MatteoAlbi/robotic-arm/python/1.jpg

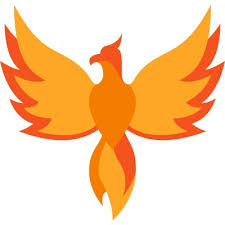
python/1.jpg
