MatteoAlbi/robotic-arm/solid works arm design/cuscinetto a sfera.SLDPRT

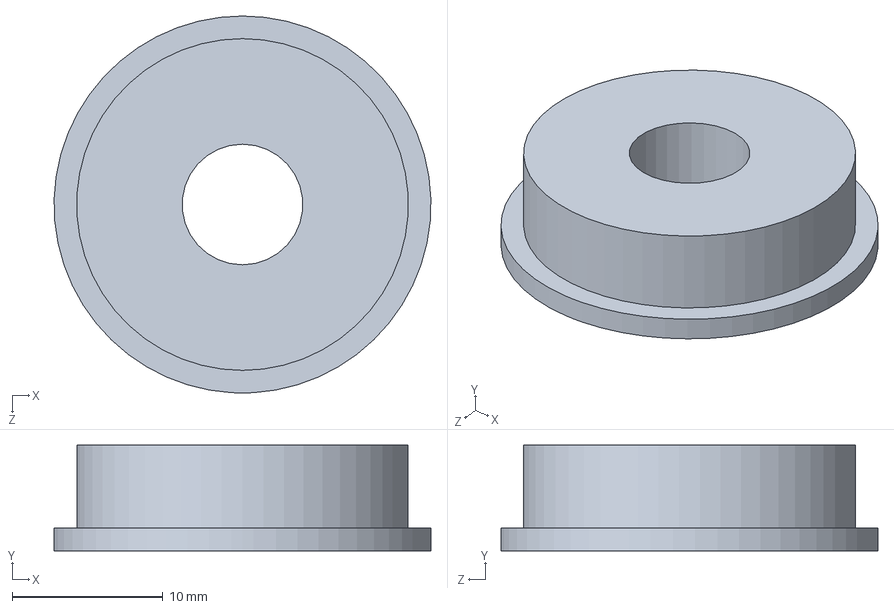
[picture p22: CAD file, 2018-10-06]
solid works arm design/cuscinetto a sfera.SLDPRT
25.0 x 7.00 x 25.0 mm
