MatteoAlbi/robotic-arm/solid works arm design/pinza motore.SLDPRT

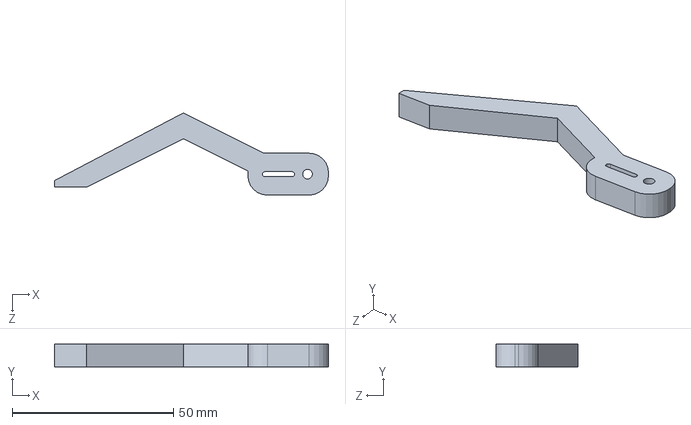
[picture p23: CAD file, 2018-10-06]
solid works arm design/pinza motore.SLDPRT
85.0 x 7.00 x 25.5 mm
