MatteoAlbi/robotic-arm/solid works arm design/aggancio penna.SLDPRT

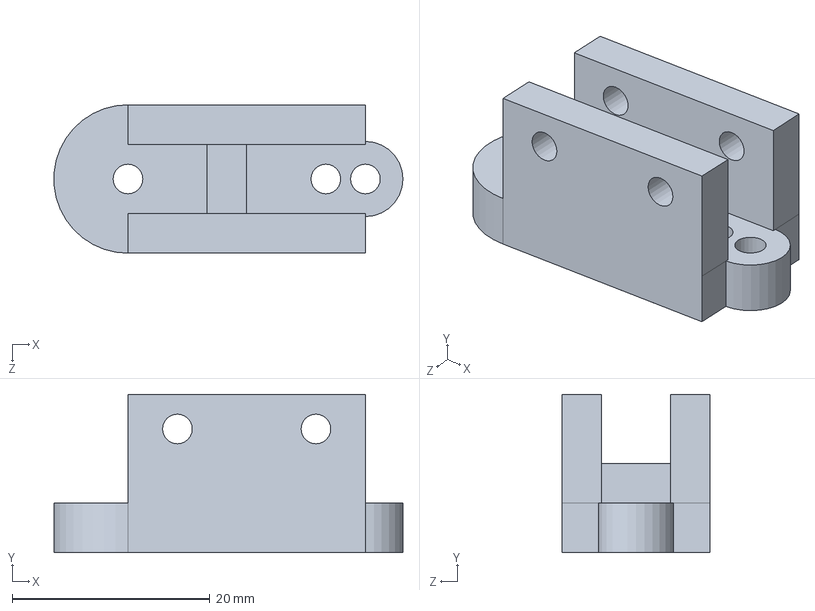
[picture p24: CAD file, 2018-10-06]
solid works arm design/aggancio penna.SLDPRT
35.3 x 16.0 x 15.0 mm
