MatteoAlbi/robotic-arm/solid works arm design/parte rotante.SLDPRT

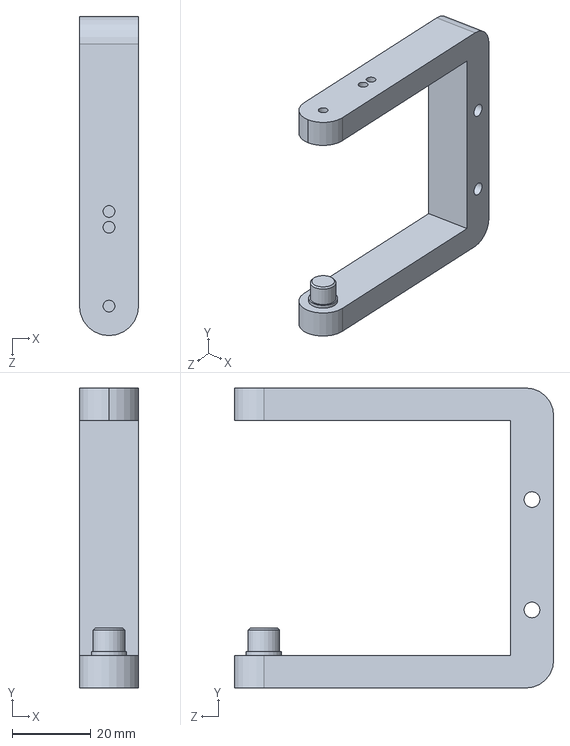
[picture p25: CAD file, 2018-10-06]
solid works arm design/parte rotante.SLDPRT
15.0 x 76.1 x 81.0 mm
