MatteoAlbi/robotic-arm/solid works arm design/pinza.SLDPRT

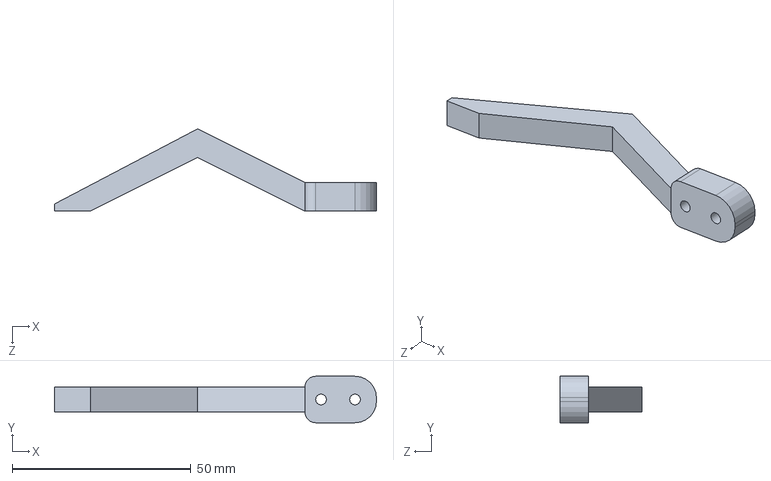
[picture p26: CAD file, 2018-10-06]
solid works arm design/pinza.SLDPRT
90.0 x 13.0 x 23.0 mm
