MatteoAlbi/robotic-arm/solid works arm design/base motore.SLDPRT

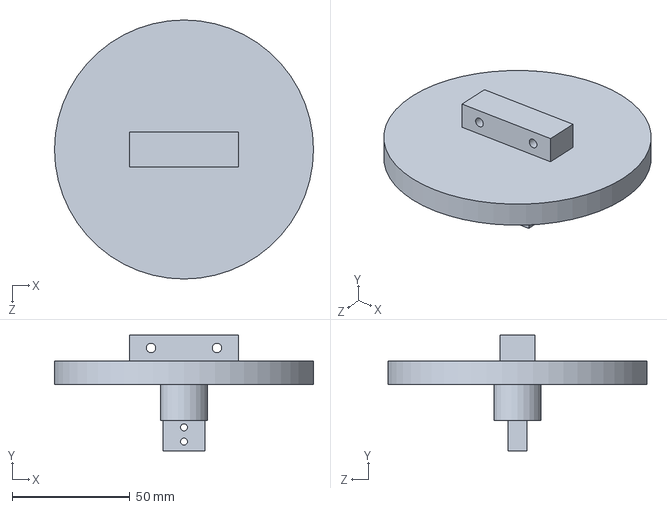
[picture p27: CAD file, 2018-10-06]
solid works arm design/base motore.SLDPRT
110.0 x 49.2 x 110.0 mm
