MatteoAlbi/robotic-arm/solid works arm design/attacco pinza.SLDPRT

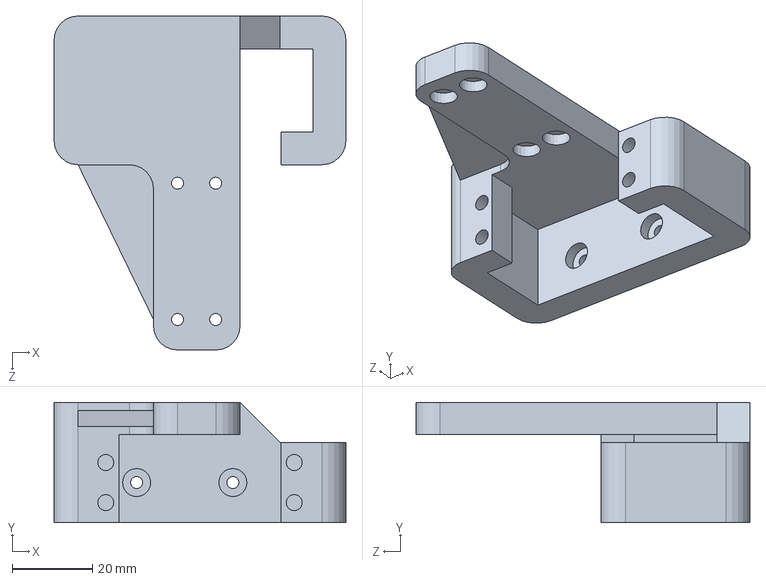
[picture p28: CAD file, 2018-10-06]
solid works arm design/attacco pinza.SLDPRT
72.8 x 30.0 x 83.3 mm
