MatteoAlbi/robotic-arm/solid works arm design/attacco penna.SLDPRT

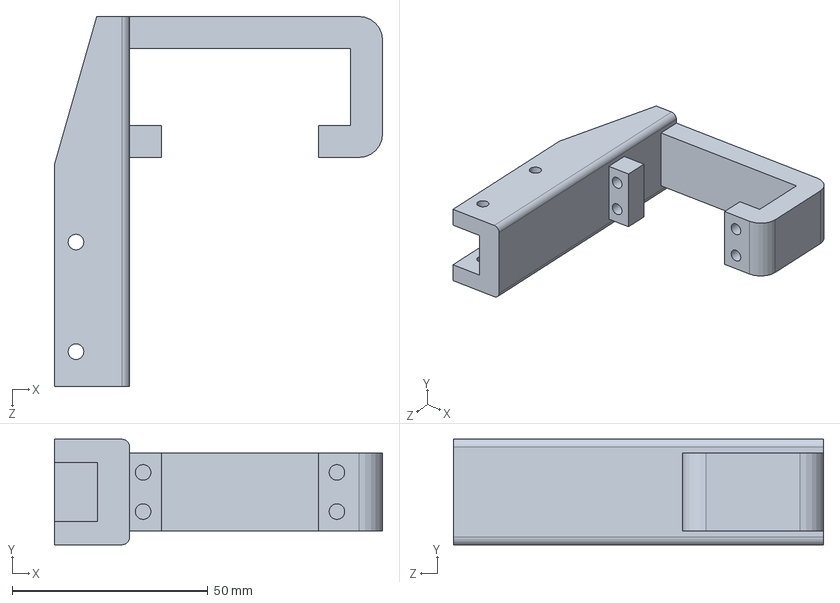
[picture p29: CAD file, 2018-10-06]
solid works arm design/attacco penna.SLDPRT
83.8 x 27.0 x 94.5 mm
